vincentgosselin1/fish_tower_v1/3.jpg

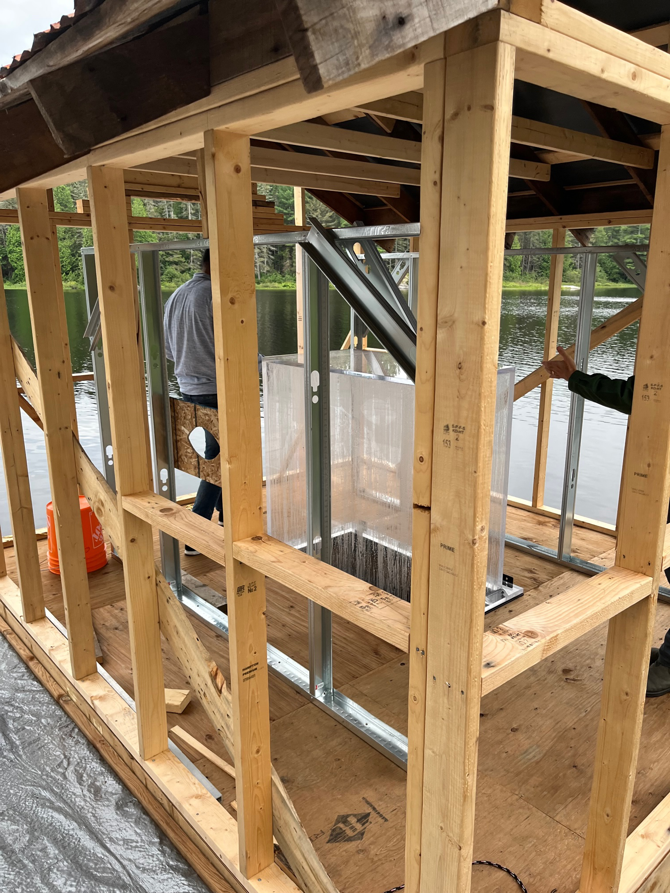
3.jpg
