vincentgosselin1/fish_tower_v1/goodtimes/02_2_corrected.jpg

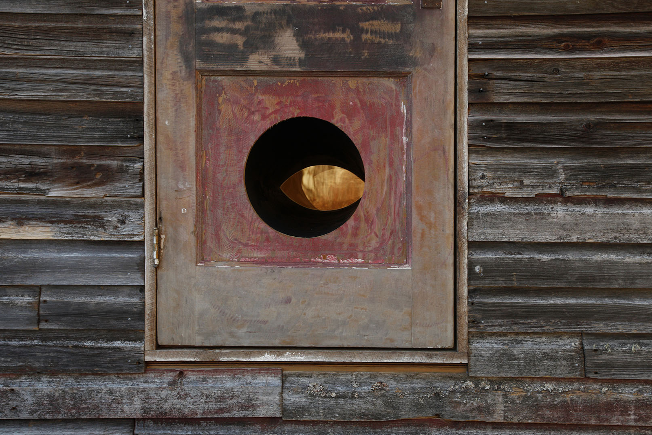
goodtimes/02_2_corrected.jpg
