vincentgosselin1/fish_tower_v1/goodtimes/03_MG_0021_corrected_1.jpg

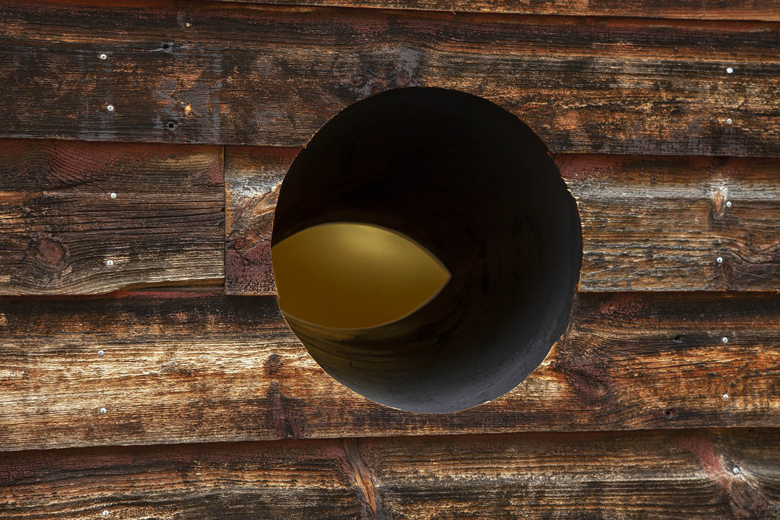
goodtimes/03_MG_0021_corrected_1.jpg
