vincentgosselin1/fish_tower_v1/goodtimes/04_Marin_Carl.jpg

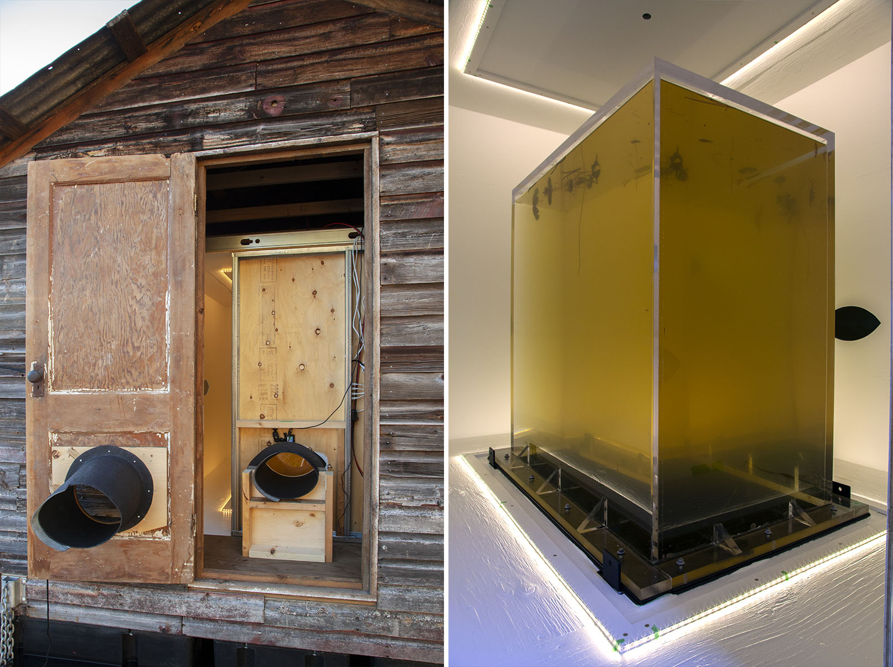
goodtimes/04_Marin_Carl.jpg
