vincentgosselin1/fish_tower_v1/goodtimes/g0000000000oodtimes4.JPG

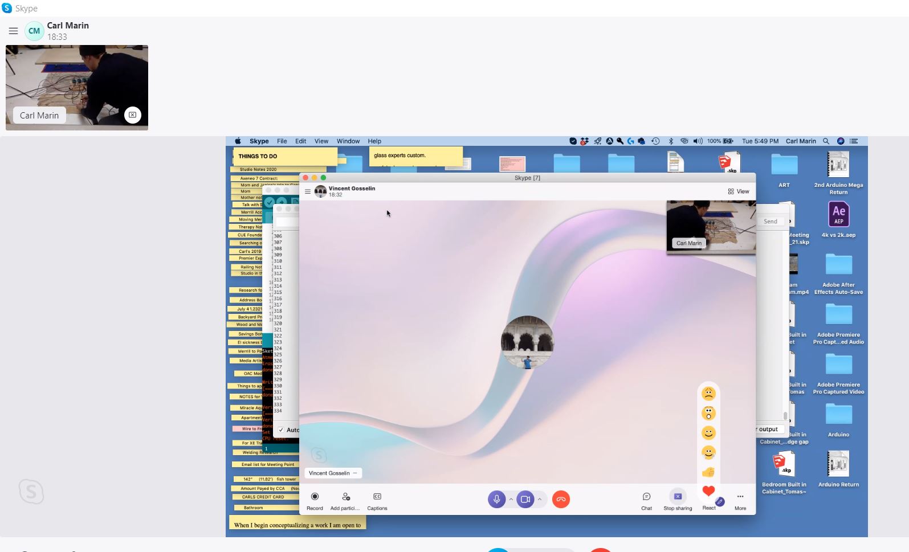
goodtimes/g0000000000oodtimes4.JPG
