vincentgosselin1/fish_tower_v1/goodtimes/goodtimes1.JPG

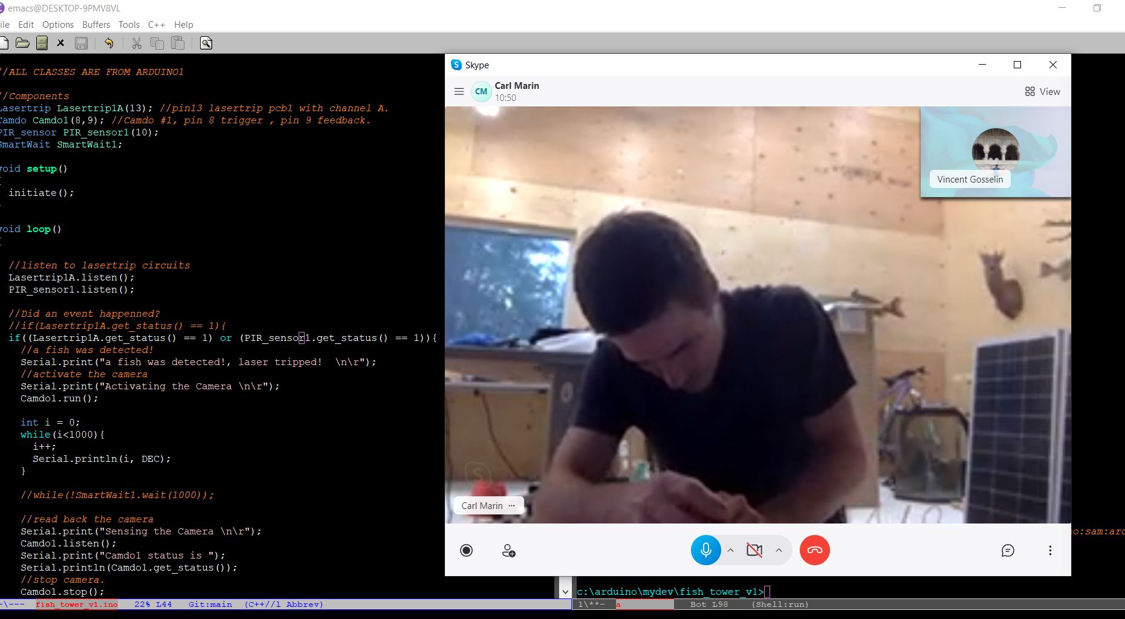
goodtimes/goodtimes1.JPG
