vincentgosselin1/fish_tower_v1/goodtimes/goodtimes2.JPG

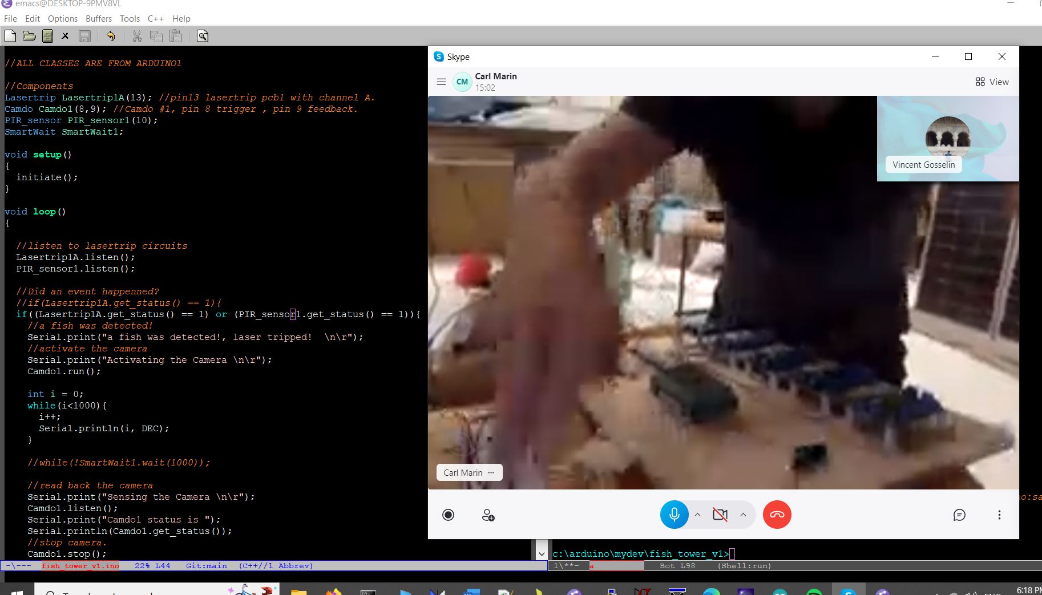
goodtimes/goodtimes2.JPG
