vincentgosselin1/fish_tower_v1/goodtimes/goodtimes3.JPG

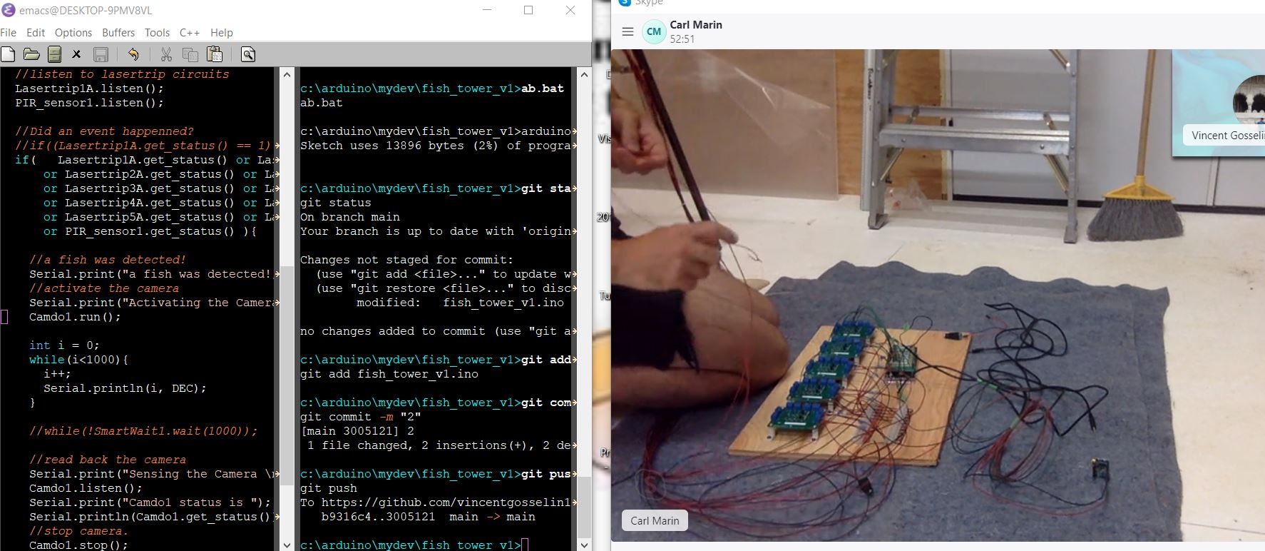
goodtimes/goodtimes3.JPG
