vincentgosselin1/fish_tower_v1/goodtimes/goodtimes4.JPG

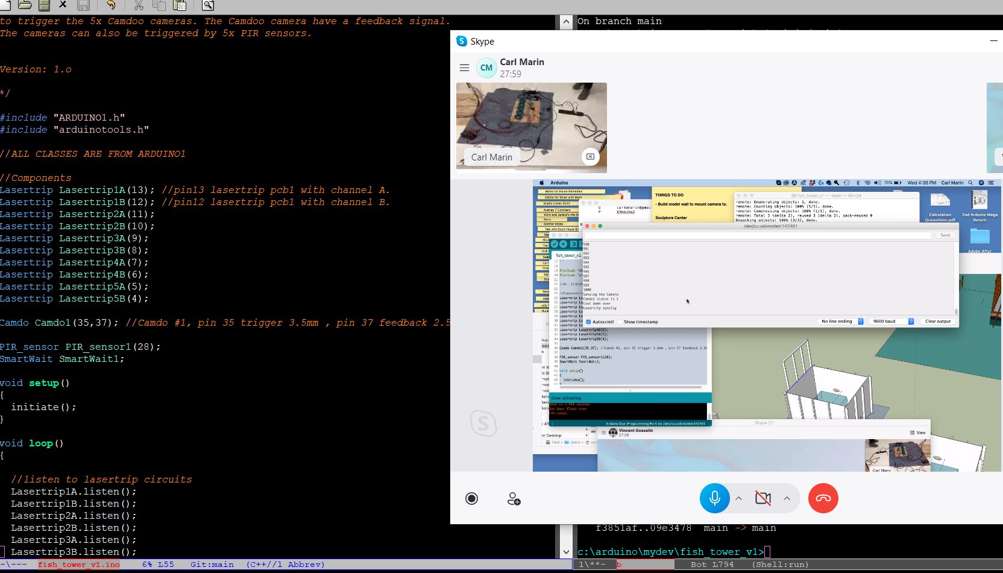
goodtimes/goodtimes4.JPG
