vincentgosselin1/fish_tower_v1/goodtimes/goodtimes.JPG

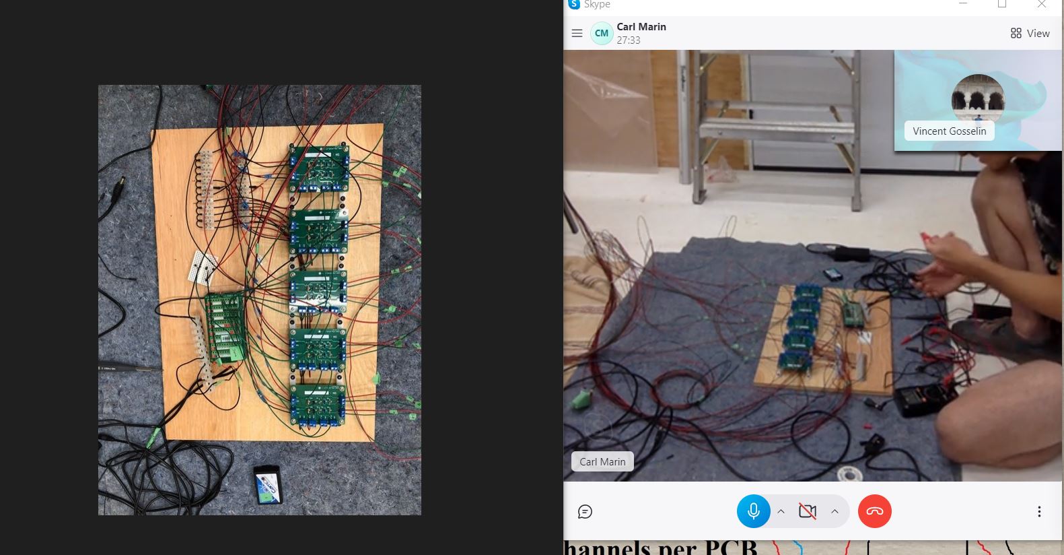
goodtimes/goodtimes.JPG
