vincentgosselin1/fish_tower_v1/goodtimes/new_arduino.JPG

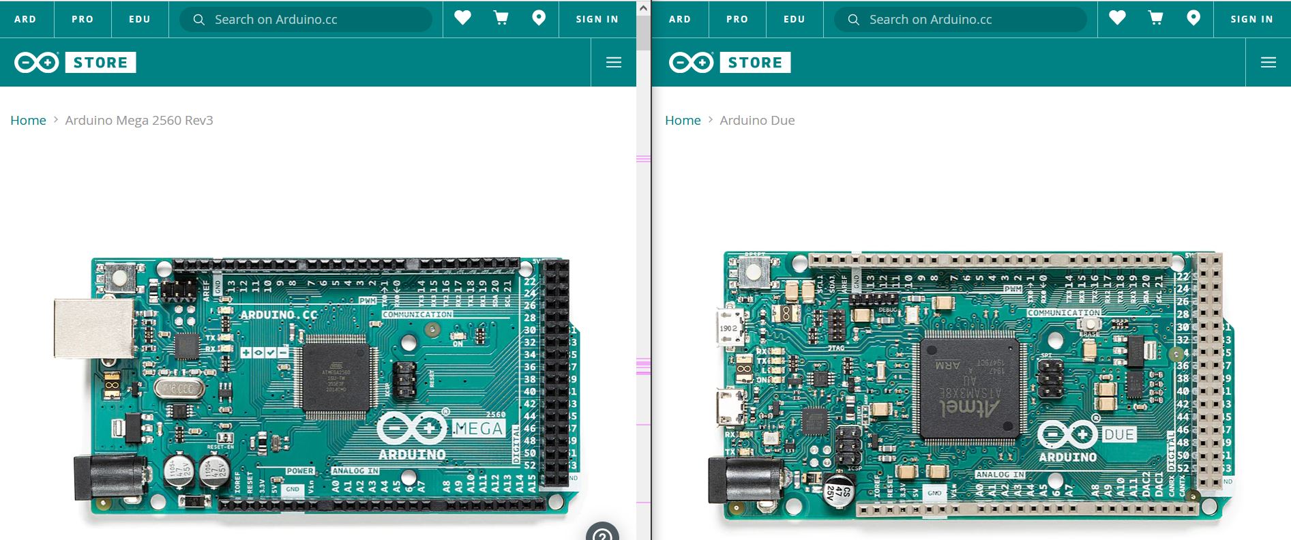
goodtimes/new_arduino.JPG
