vincentgosselin1/fish_tower_v1/Laser_trip_circuit_v1/art.png

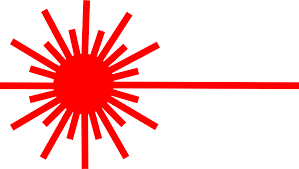
Laser_trip_circuit_v1/art.png
