vincentgosselin1/fish_tower_v1/Laser_trip_circuit_v1/laser_trip_circuit_v1.JPG

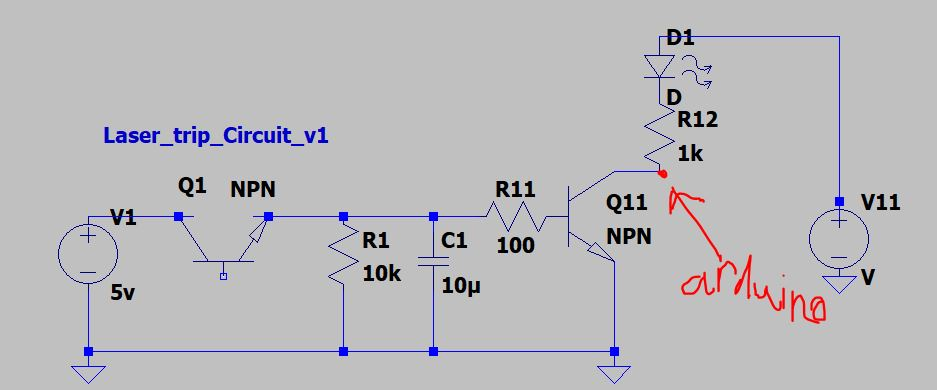
Laser_trip_circuit_v1/laser_trip_circuit_v1.JPG
