vincentgosselin1/fish_tower_v1/Laser_trip_circuit_v1/ltspice/Laser_trip_circuit_v1.asc

C1: cap; 10µ
D1: LED
Q1: npn
Q11: npn
R1: res; 10k
R11: res; 100
R12: res; 1k
V1: voltage; 5v
V11: voltage; 5
V12: voltage; PULSE(5 0 0.1 0.01 0.01 0.1)
Named nets: 0, vp, chanA
Laser_trip_Circuit_v1
.tran 1
